bzgec/esp32_display/Simulations/inrush_current_limiter/inrush_current_limiter.asc

C1: cap; 0.1µ
C2: cap; {C_load}
C3: cap; {C_source}
C4: cap; {C_source}
C6: cap; {C_load}
D1: zener; DI_MMSZ5232B
L1: ind; 10µ
M1: pmos; DMG2301L
R1: res; 100k
R2: res; {R_load}
R3: res; {R_source}
R4: res; 10Meg
R5: res; 10Meg
R6: res; {R_source}
R7: res; 10Meg
R8: res; 10Meg
R10: res; {R_load}
S1: sw; SW1
S2: sw; SW1
V2: voltage; PULSE(0 200 1u 10n 10n 5m 10m 10)
V_iout_L: voltage; 0
V_iout_MOS: voltage; 0
V_L: voltage; 5
V_MOS: voltage; 5
Named nets: 0, Vin_MOS, Vout_MOS, Vsw, Vgate, Vout_L, Vin_L
.tran 0 20m 0 1u startup
.model SW1 SW(Ron=1f Roff=10Meg Vt=100 Vh=10)
*---------- DMG2301L Spice Model ----------
.SUBCKT DMG2301L 10 20 30 
*     TERMINALS:  D  G  S
M1 1 2 3 3 PMOS L = 1E-006 W = 1E-006 
RD 10 1 0.08416 
RS 30 3 0.001 
RG 20 2 40.9 
CGS 2 3 1.265E-010 
EGD 12 30 2 1 1 
VFB 14 30 0 
FFB 2 1 VFB 1 
CGD 13 14 1.85E-010 
R1 13 30 1 
D1 13 12 DLIM 
DDG 14 15 DCGD 
R2 12 15 1 
D2 30 15 DLIM 
DSD 10 3 DSUB 
.MODEL PMOS PMOS LEVEL = 3 U0 = 400 VMAX = 1E+006 ETA = 0.001 
+ TOX = 6E-008 NSUB = 1E+016 KP = 6.629 KAPPA = 19.32 VTO = -0.6459 
.MODEL DCGD D CJO = 1.177E-010 VJ = 0.611 M = 0.6 
.MODEL DSUB D IS = 0.0001419 N = 4.041 RS = 7.253E-009 BV = 22 CJO = 2.853E-011 VJ = 0.7195 M = 0.6 
.MODEL DLIM D IS = 0.0001 
.ENDS
*Diodes DMG2301L Spice Model v1.0M Last Revised 2018/2/1
.op
.tran 0 3m 0 0.1u startup
.param C_load 50u
.param R_load 25
.param R_source 0.3
.param C_source 10u
*SRC=MMSZ5232B;DI_MMSZ5232B;Diodes;Zener <=10V; 5.60V  0.500W   Diodes Inc. 500 mW Zener
*SYM=HZEN
.SUBCKT DI_MMSZ5232B  1 2
*        Terminals    A   K
D1 1 2 DF
DZ 3 1 DR
VZ 2 3 3.23
.MODEL DF D ( IS=36.8p RS=34.7 N=1.10
+ CJO=106p VJ=0.750 M=0.330 TT=50.1n )
.MODEL DR D ( IS=7.36f RS=7.11 N=3.00 )
